bdurrett/BART-watcher-ESP8266/assets/images/BART watcher Case with OLED and button.jpg

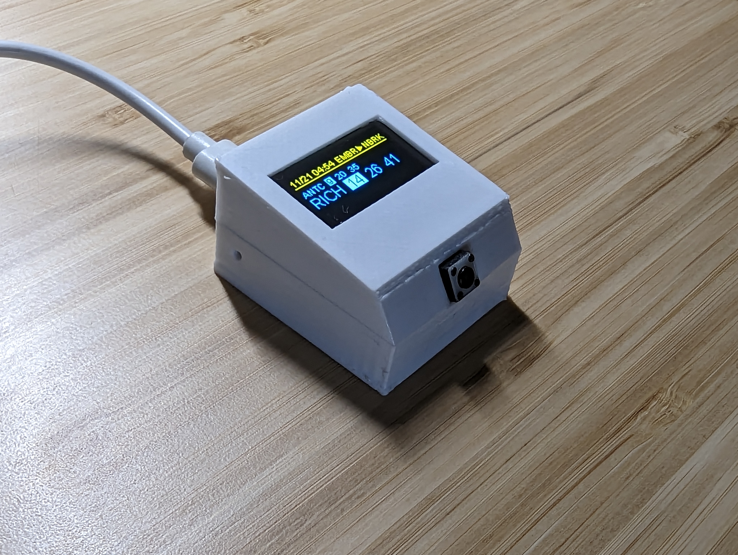
assets/images/BART watcher Case with OLED and button.jpg
