bdurrett/BART-watcher-ESP8266/assets/images/BART watcher display screen.png

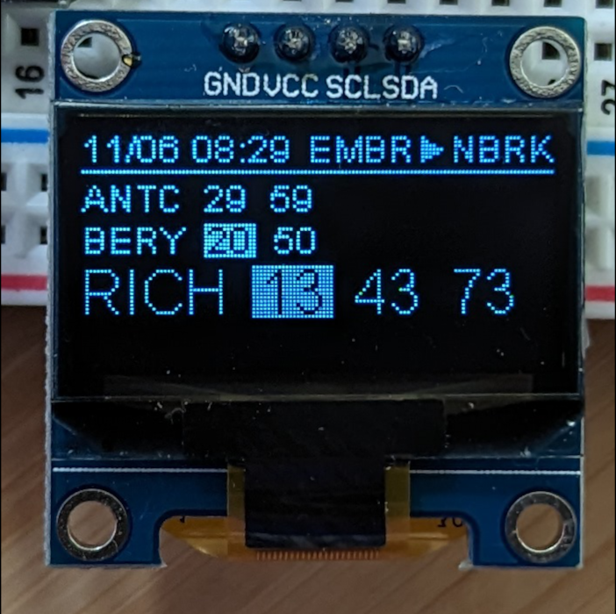
assets/images/BART watcher display screen.png
