bdurrett/BART-watcher-ESP8266/assets/images/ESP8266_oled_display_wiring.png

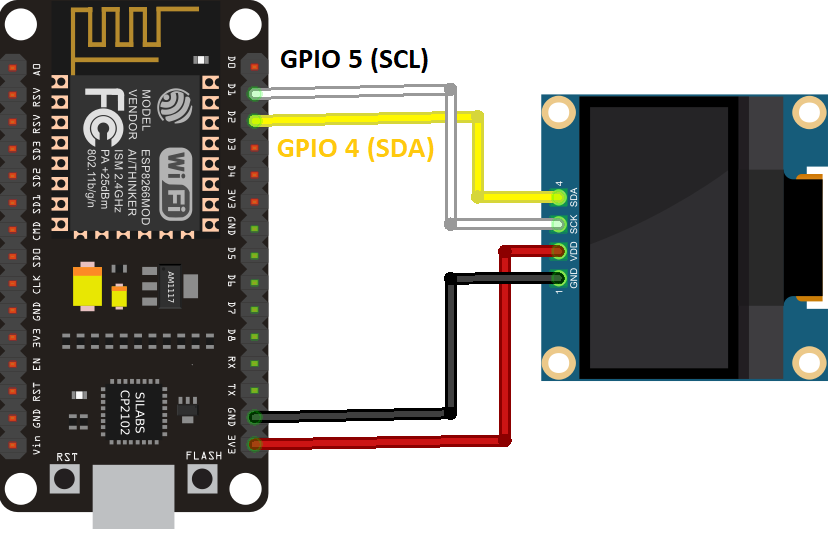
assets/images/ESP8266_oled_display_wiring.png
